anroots/tiny-doorbell-remote/img/arduino_prototype.jpg

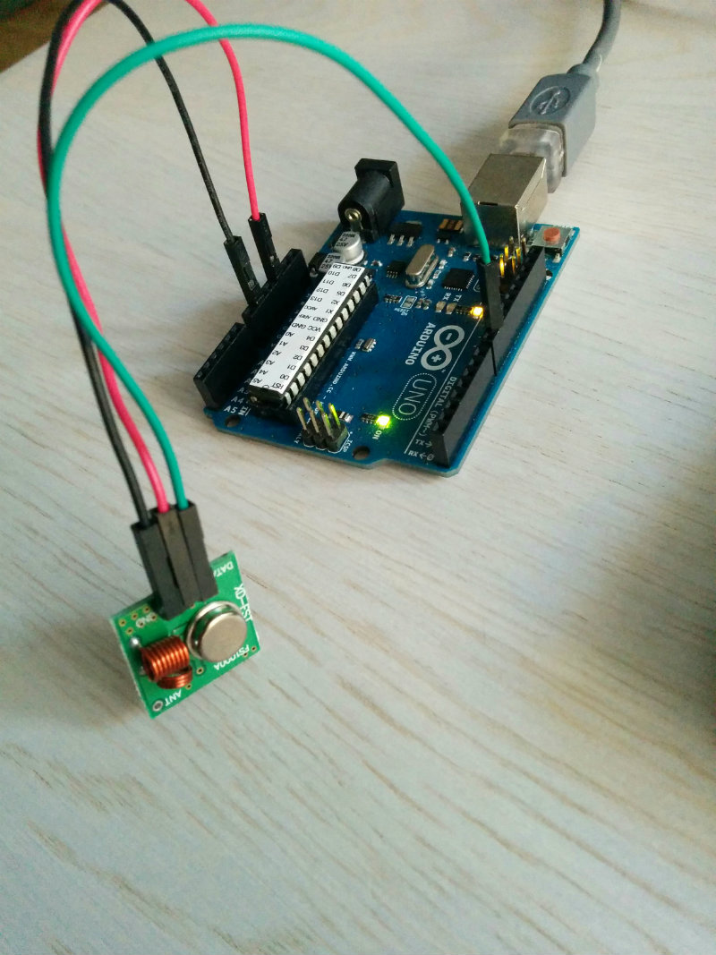
img/arduino_prototype.jpg
