anroots/tiny-doorbell-remote/img/doorbell_back.jpg

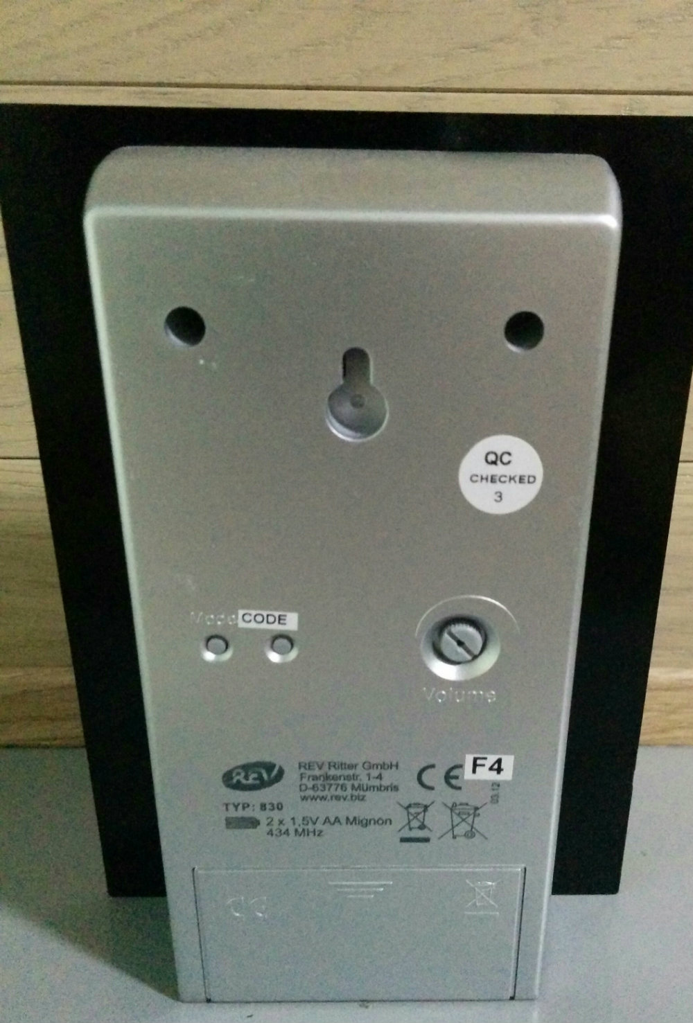
img/doorbell_back.jpg
