anroots/tiny-doorbell-remote/img/doorbell_button.jpg

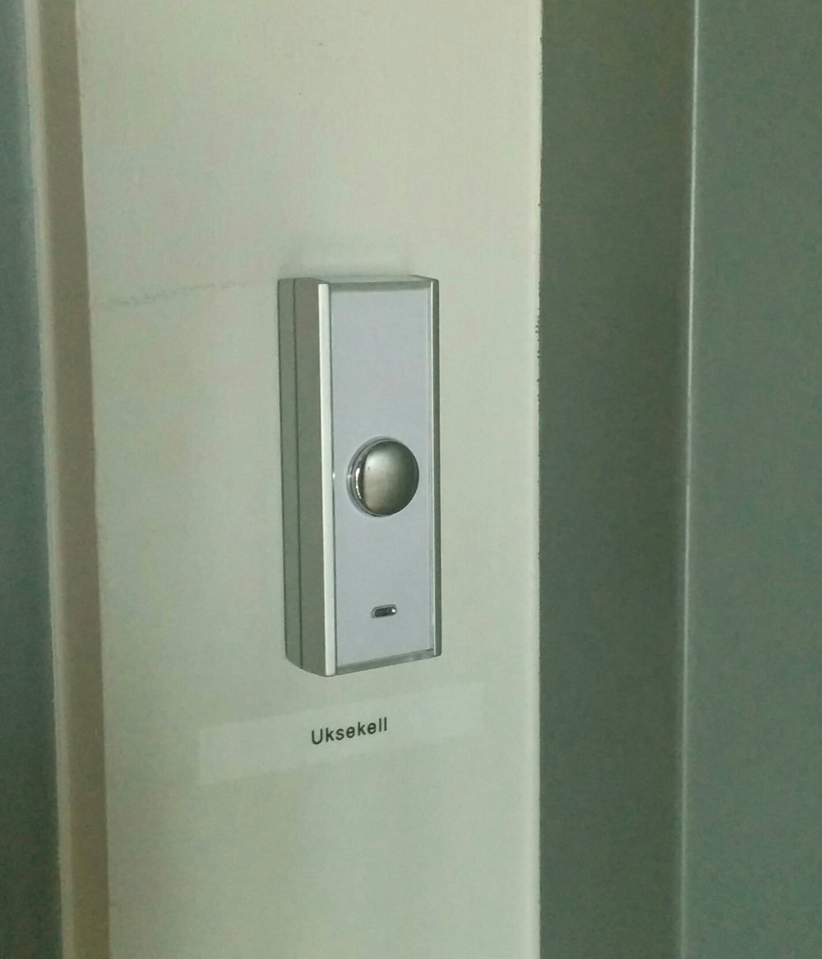
img/doorbell_button.jpg
