anroots/tiny-doorbell-remote/img/module_back.jpg

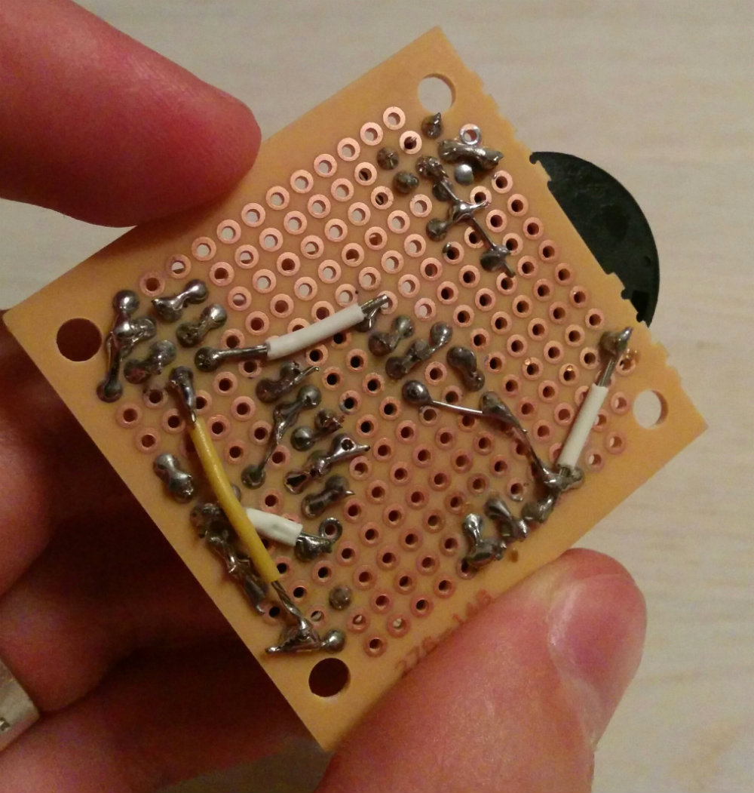
img/module_back.jpg
