anroots/tiny-doorbell-remote/img/module_brushing.jpg

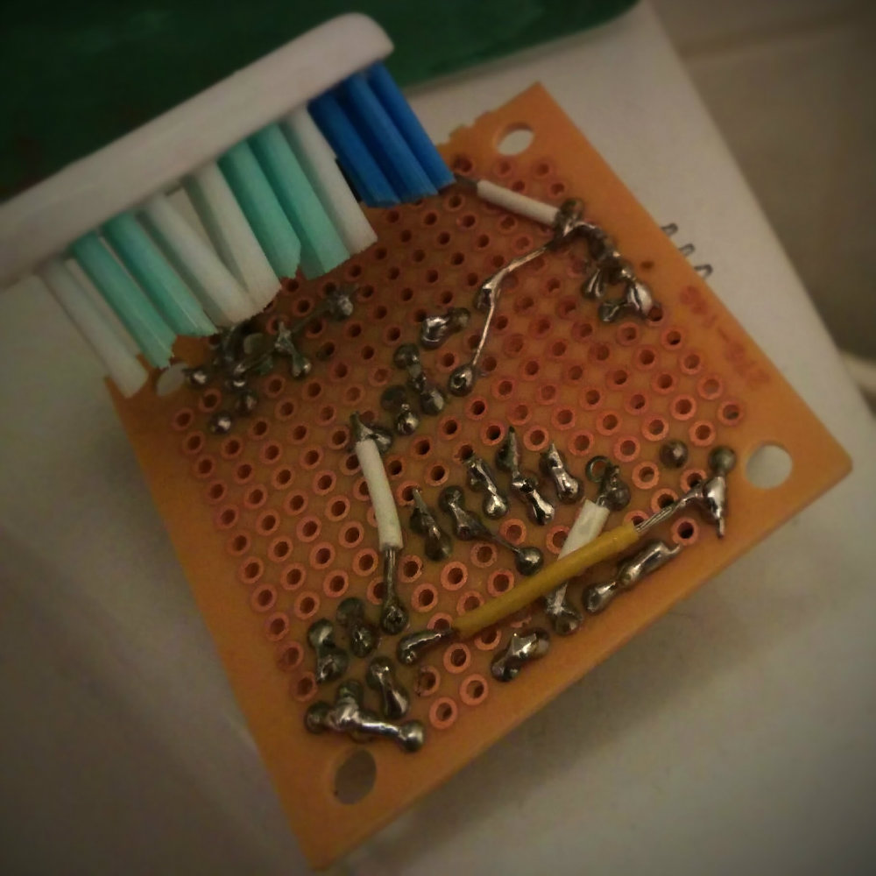
img/module_brushing.jpg
