anroots/tiny-doorbell-remote/img/module_programming.jpg

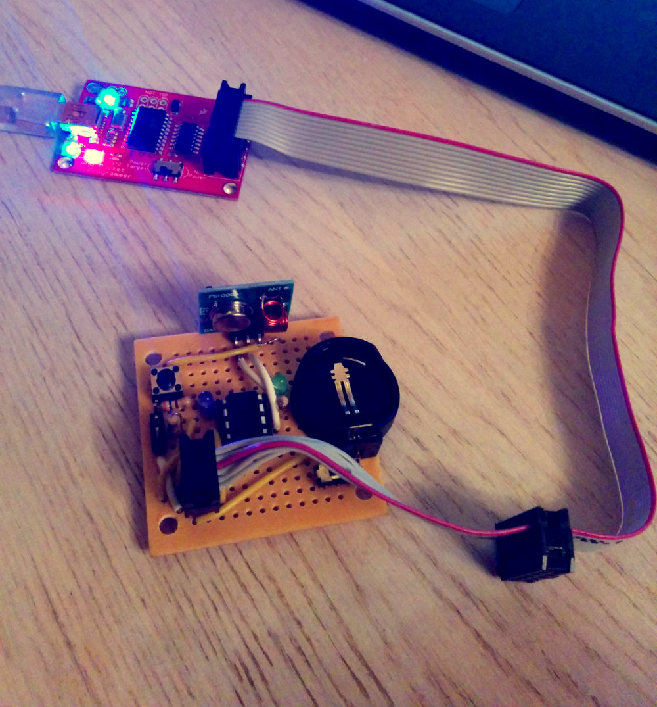
img/module_programming.jpg
