anroots/tiny-doorbell-remote/img/replicating_signal1.png

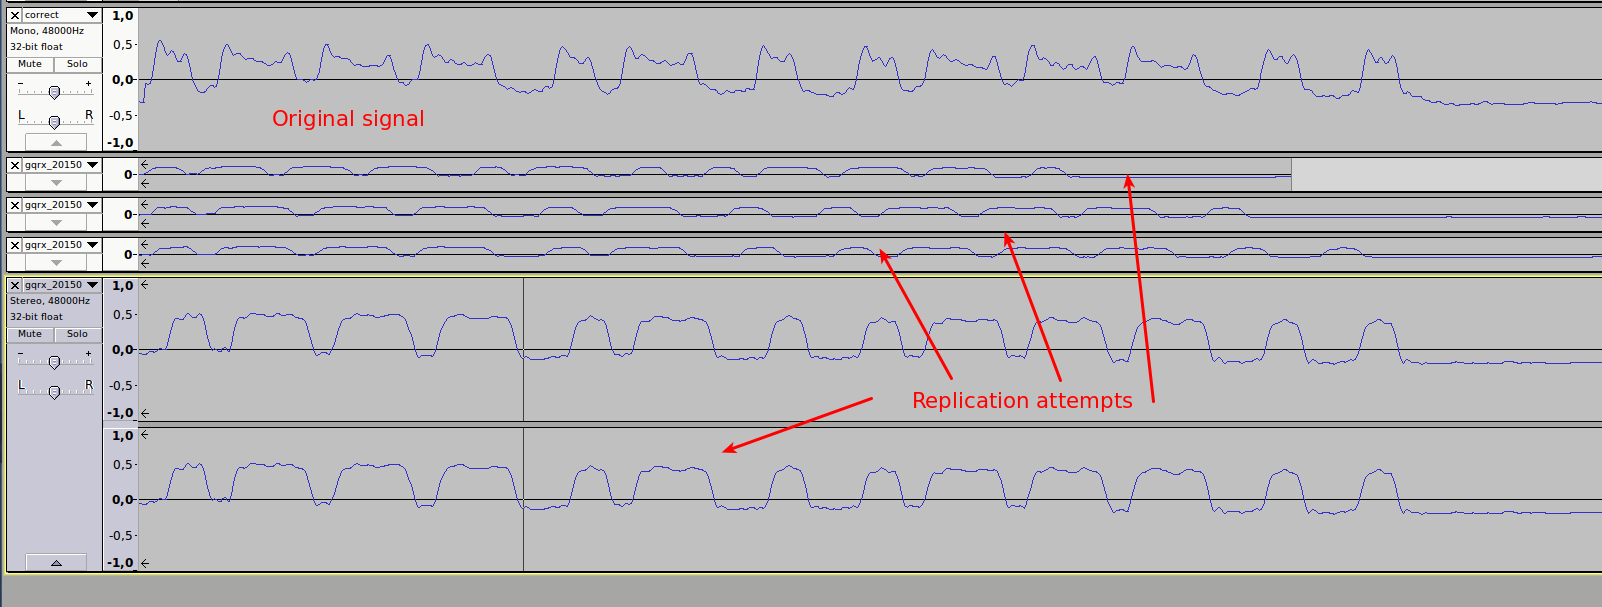
img/replicating_signal1.png
