anroots/tiny-doorbell-remote/img/signal_comparison_inverse.jpg

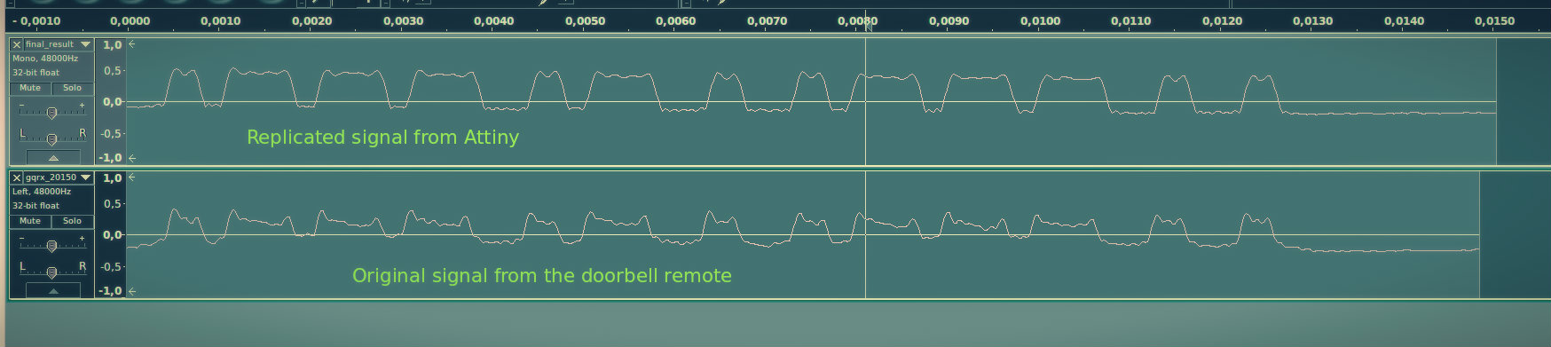
img/signal_comparison_inverse.jpg
