anroots/tiny-doorbell-remote/img/working_desk.jpg

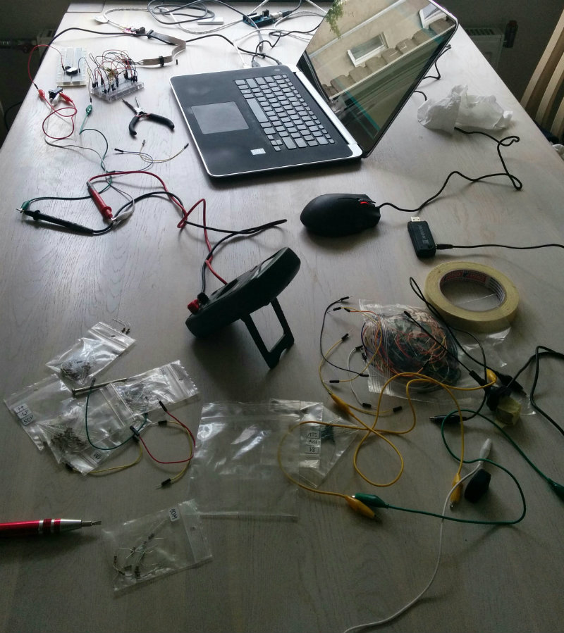
img/working_desk.jpg
